Il-Minguz/rolling-code-briefcase/hardware/pcb-v2-through-hole/gerbers/GBR_7031061_1_snapshot.png

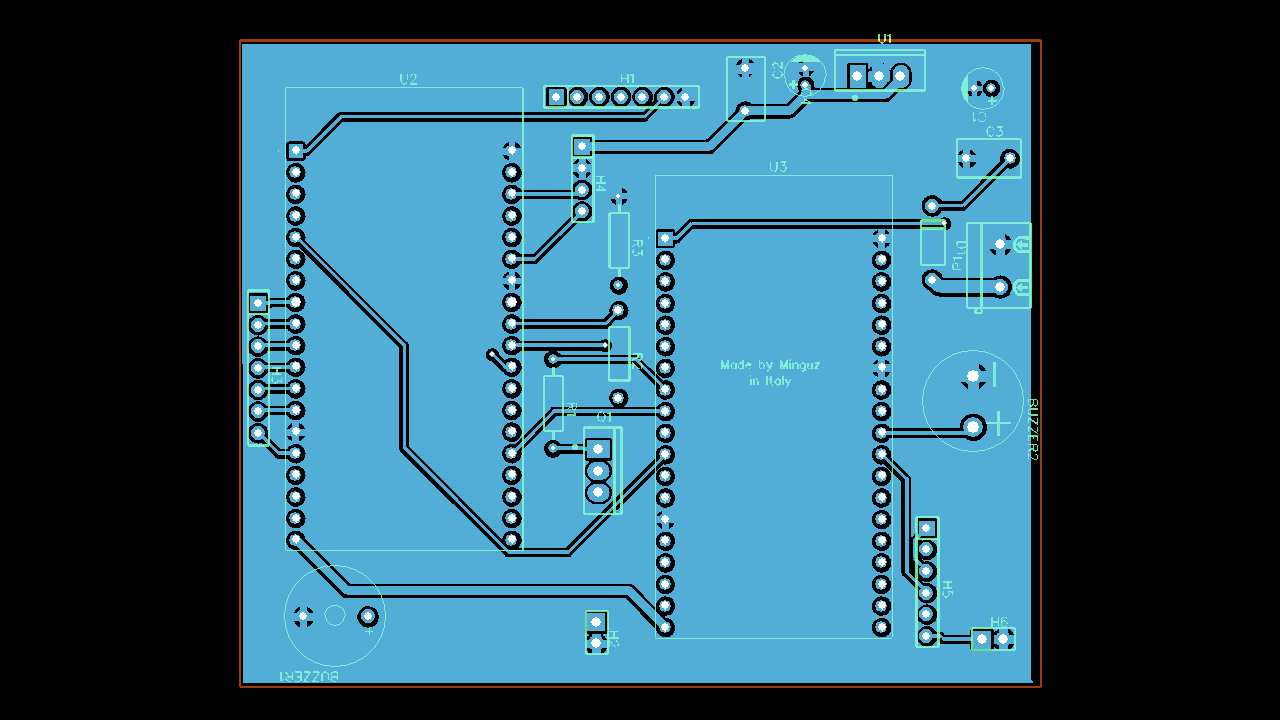
hardware/pcb-v2-through-hole/gerbers/GBR_7031061_1_snapshot.png
