Il-Minguz/rolling-code-briefcase/hardware/pcb-v2-through-hole/gerbers/ul_bo.png

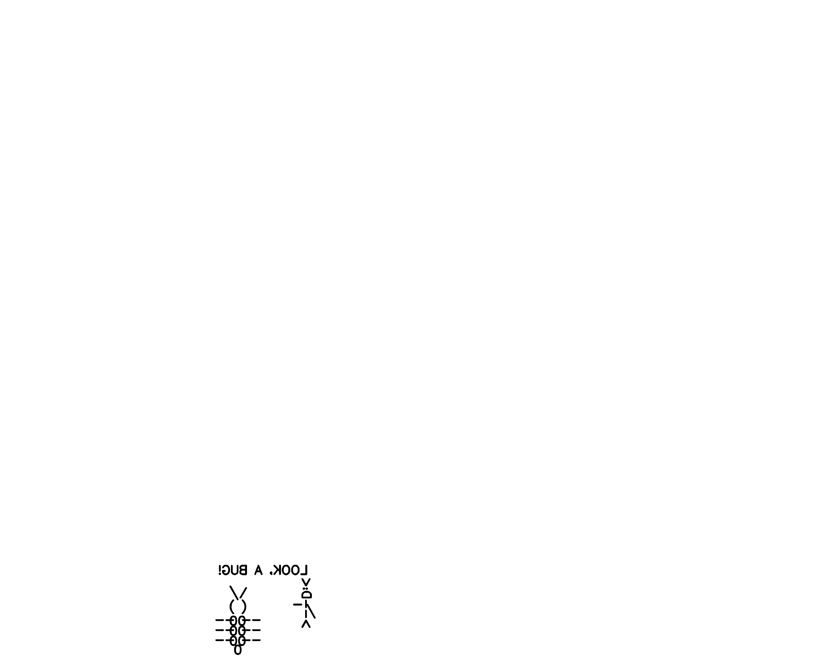
hardware/pcb-v2-through-hole/gerbers/ul_bo.png
