Il-Minguz/rolling-code-briefcase/hardware/pcb-v2-through-hole/gerbers/ul_to.png

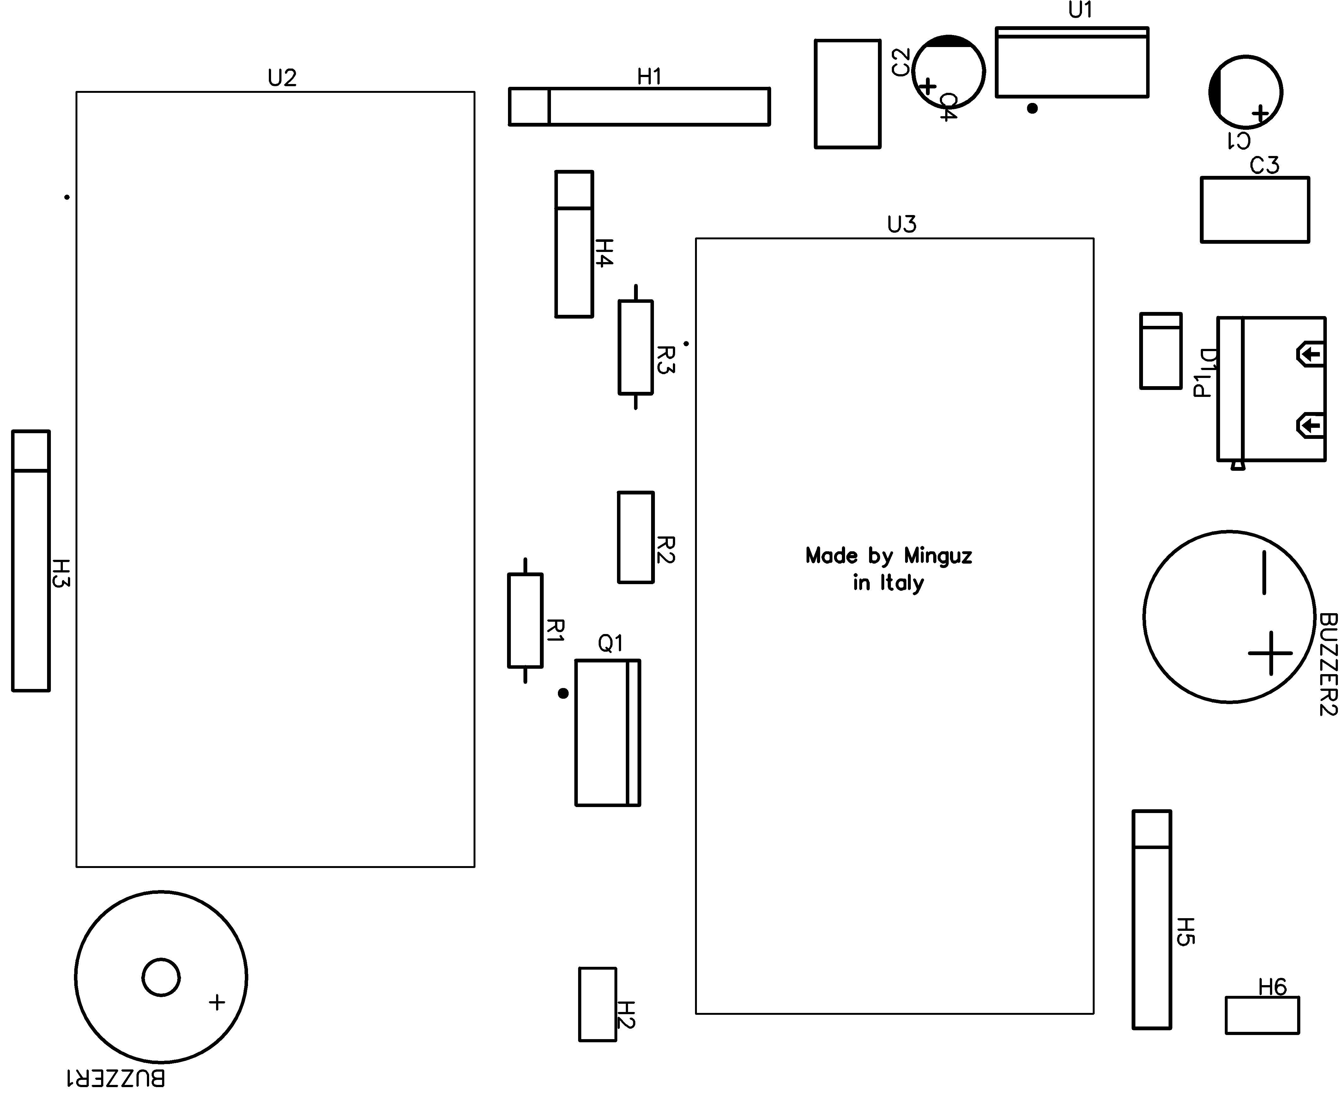
hardware/pcb-v2-through-hole/gerbers/ul_to.png
