Il-Minguz/rolling-code-briefcase/media/photos/extern-unit-internals.jpg

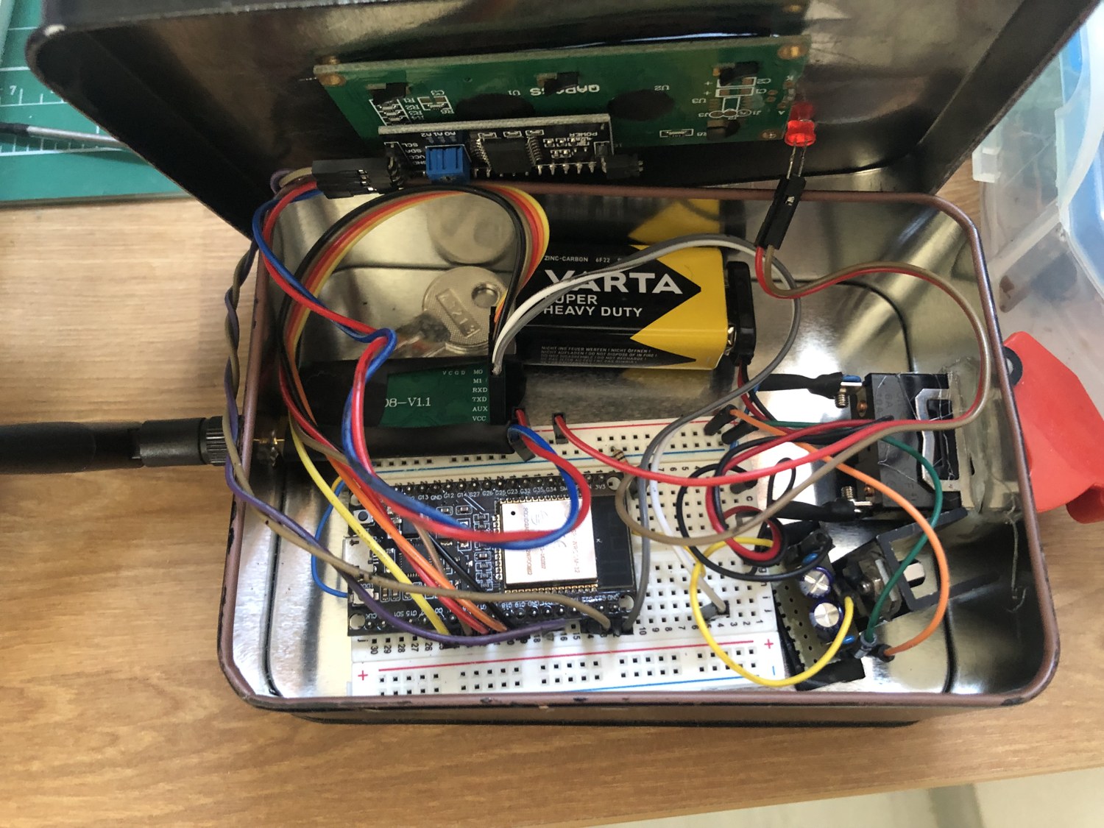
media/photos/extern-unit-internals.jpg
