Il-Minguz/rolling-code-briefcase/media/photos/psu-module.jpg

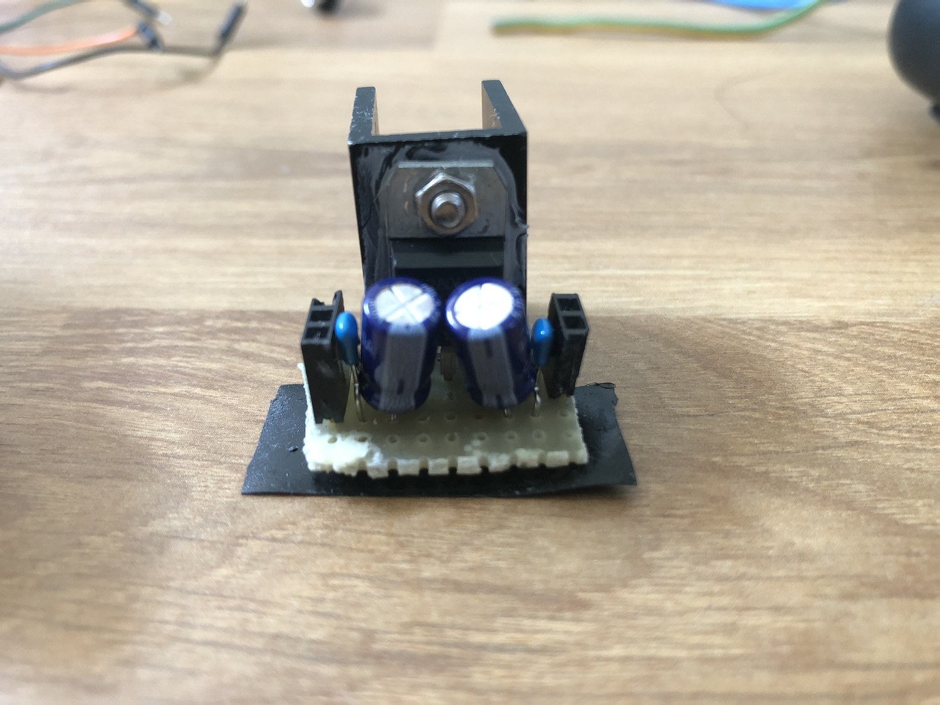
media/photos/psu-module.jpg
