Il-Minguz/rolling-code-briefcase/media/photos/transmitter-detail.jpg

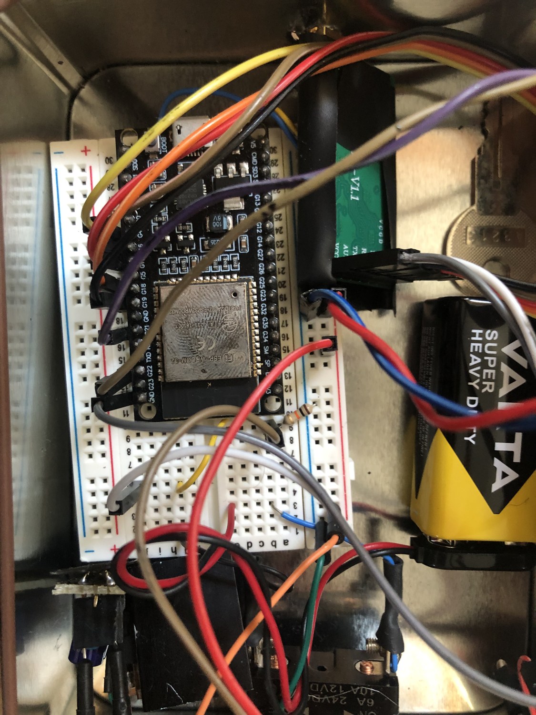
media/photos/transmitter-detail.jpg
