Il-Minguz/rolling-code-briefcase/media/photos/transmitter-lcd.jpg

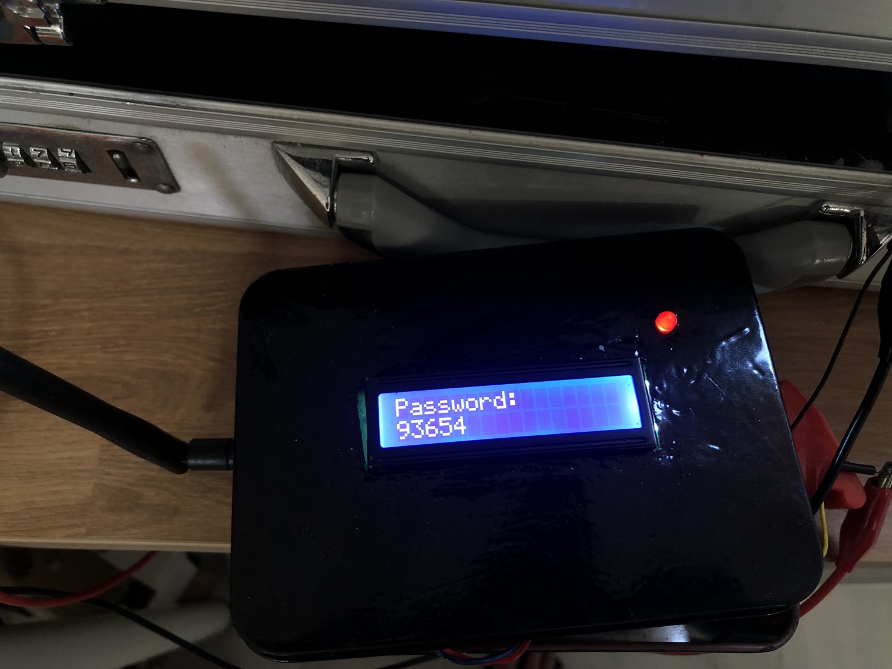
media/photos/transmitter-lcd.jpg
