Il-Minguz/rolling-code-briefcase/media/photos/transmitter-open.jpg

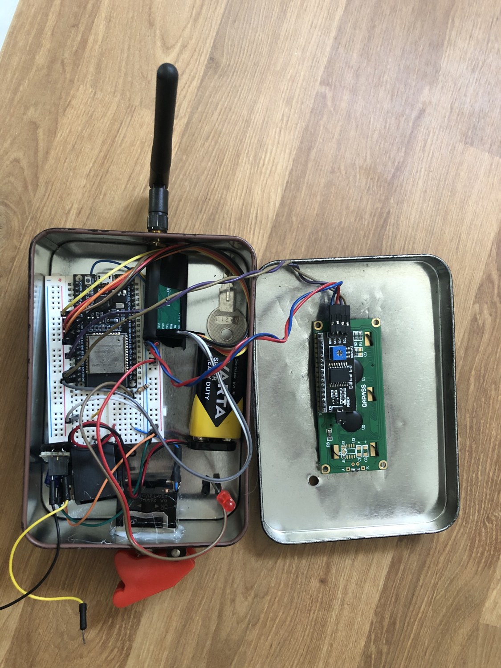
media/photos/transmitter-open.jpg
